I-am-Chittesh/JARVIS/Hardware/PCB/Jarvis_v1.kicad_sch

## KiCad design Hardware/PCB/Jarvis_v1.kicad_sch (2026-02-18)

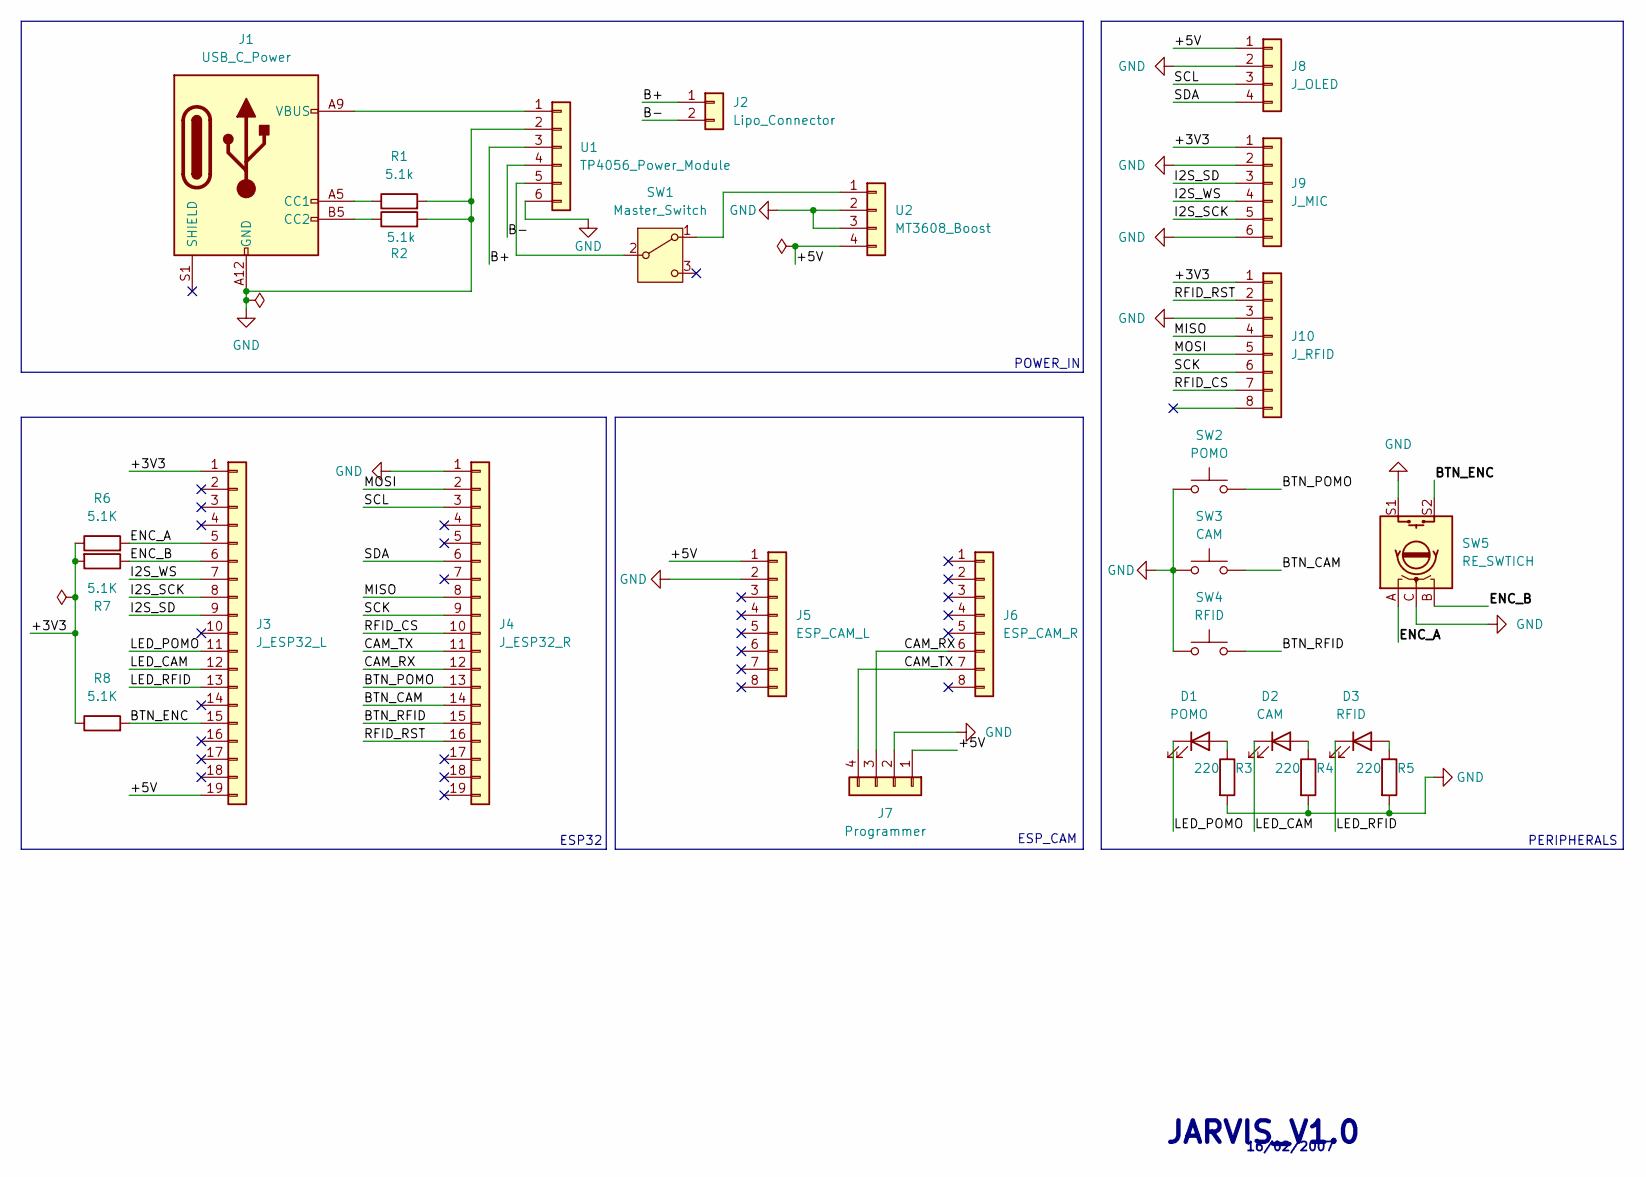
[picture p2: schematic Jarvis_v1.kicad_sch]

Parts:
D1: POMO; LED_D3.0mm
D2: CAM; LED_D3.0mm
D3: RFID; LED_D3.0mm
J1: USB_C_Power; USB_C_Receptacle_GCT_USB4125-xx-x_6P_TopMnt_Horizontal
J2: Lipo_Connector; JST_PH_S2B-PH-K_1x02_P2.00mm_Horizontal
J3: J_ESP32_L; PinHeader_1x19_P2.54mm_Vertical
J4: J_ESP32_R; PinHeader_1x19_P2.54mm_Vertical
J5: ESP_CAM_L; PinHeader_1x08_P2.54mm_Vertical
J6: ESP_CAM_R; PinHeader_1x08_P2.54mm_Vertical
J7: Programmer; PinHeader_1x04_P2.54mm_Vertical
J8: J_OLED; PinHeader_1x04_P2.54mm_Vertical
J9: J_MIC; PinHeader_1x06_P2.54mm_Vertical
J10: J_RFID; PinHeader_1x08_P2.54mm_Vertical
R1, R2: 5.1k; R_Axial_DIN0207_L6.3mm_D2.5mm_P7.62mm_Horizontal
R3, R4, R5: 220; R_Axial_DIN0207_L6.3mm_D2.5mm_P7.62mm_Horizontal
R6, R7, R8: 5.1K; R_Axial_DIN0207_L6.3mm_D2.5mm_P7.62mm_Horizontal
SW1: Master_Switch; PinHeader_1x03_P2.54mm_Vertical
SW2: POMO; SW_PUSH_6mm_H5mm
SW3: CAM; SW_PUSH_6mm_H5mm
SW4: RFID; SW_PUSH_6mm_H5mm
SW5: RE_SWTICH; RotaryEncoder_Alps_EC11E-Switch_Vertical_H20mm
U1: TP4056_Power_Module; PinHeader_1x06_P2.54mm_Vertical
U2: MT3608_Boost; PinHeader_1x04_P2.54mm_Vertical

Connections:
+3V3: J3.1, J9.1, J10.1, R6.1, R7.2, R8.1
+5V: J3.19, J5.1, J7.1, J8.1, U2.4
B+: J2.1, U1.3
B-: J2.2, U1.4
BTN_CAM: J4.14, SW3.2
BTN_ENC: J3.15, R8.2, SW5.S2
BTN_POMO: J4.13, SW2.2
BTN_RFID: J4.15, SW4.2
CAM_RX: J4.12, J6.6, J7.3
CAM_TX: J4.11, J6.7, J7.4
ENC_A: J3.5, R6.2, SW5.A
ENC_B: J3.6, R7.1, SW5.B
GND: J1.A12 (GND), J1.B12 (GND), J4.1, J5.2, J7.2, J8.2, J9.2, J9.6, J10.3, R1.2, R2.2, R3.2, R4.2, R5.2, SW2.1, SW3.1, SW4.1, SW5.C, SW5.S1, U1.2, U1.6, U2.2, U2.3
I2S_SCK: J3.8, J9.5
I2S_SD: J3.9, J9.3
I2S_WS: J3.7, J9.4
LED_CAM: D2.1 (K), J3.12
LED_POMO: D1.1 (K), J3.11
LED_RFID: D3.1 (K), J3.13
MISO: J4.8, J10.4
MOSI: J4.2, J10.5
unnamed: D1.2 (A), R3.1
unnamed: D2.2 (A), R4.1
unnamed: D3.2 (A), R5.1
unnamed: J1.A5 (CC1), R1.1
unnamed: J1.A9 (VBUS), J1.B9 (VBUS), U1.1
unnamed: J1.B5 (CC2), R2.1
unnamed: SW1.1 (A), U2.1
unnamed: SW1.2 (B), U1.5
RFID_CS: J4.10, J10.7
RFID_RST: J4.16, J10.2
SCK: J4.9, J10.6
SCL: J4.3, J8.3
SDA: J4.6, J8.4

Notes on the sheet:
16/02/2007
ESP_CAM
POWER_IN
JARVIS_V1.0
ESP32
PERIPHERALS
